AleksandrDneprCity/Pentagon-4096/Firmwares/PS2_Mouse/ATTiny2313/ZXKM4.PNG

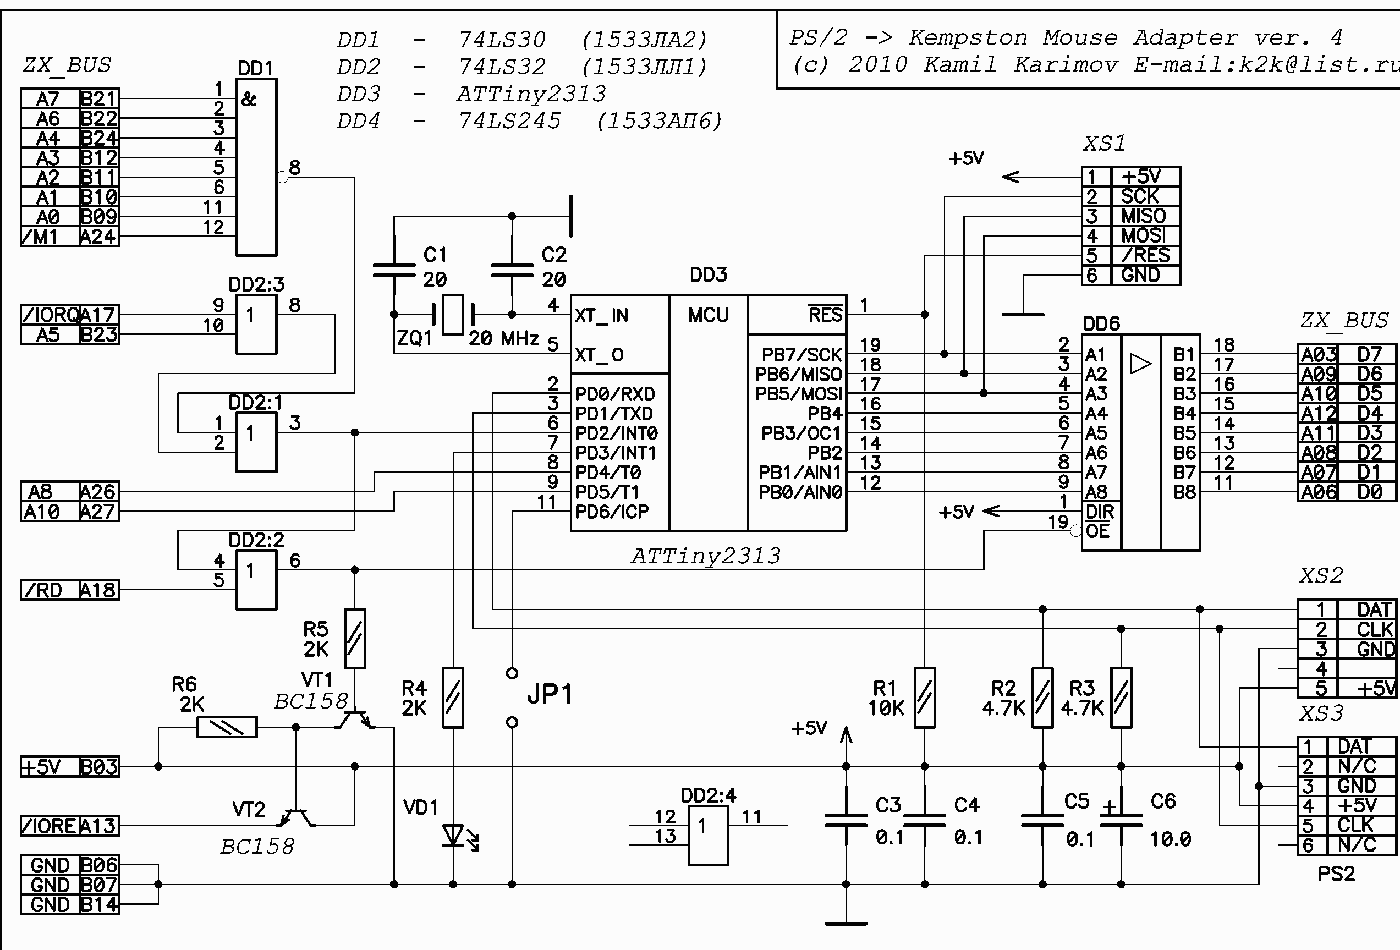
Firmwares/PS2_Mouse/ATTiny2313/ZXKM4.PNG
