AleksandrDneprCity/Pentagon-4096/H_Sign_Multisim.png

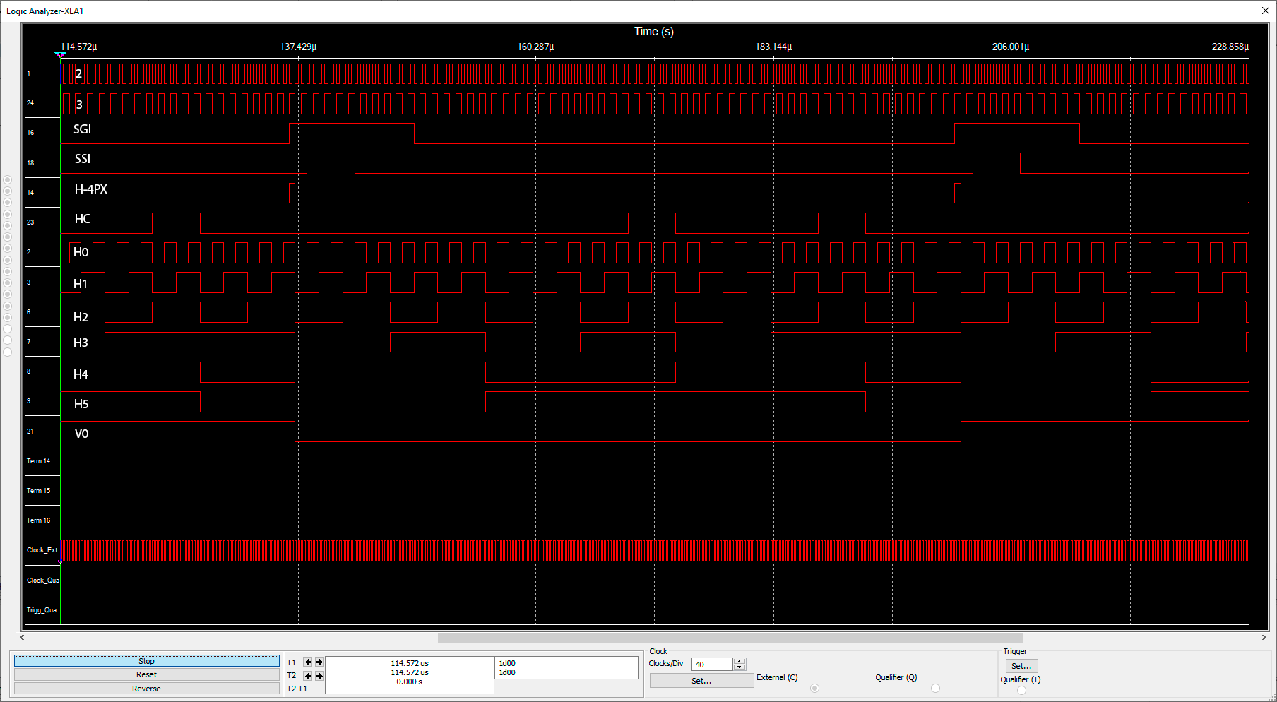
H_Sign_Multisim.png
