AleksandrDneprCity/Pentagon-4096/Hardware/Export/PNG/FreqInd-v1-pcb-comp-bottom.png

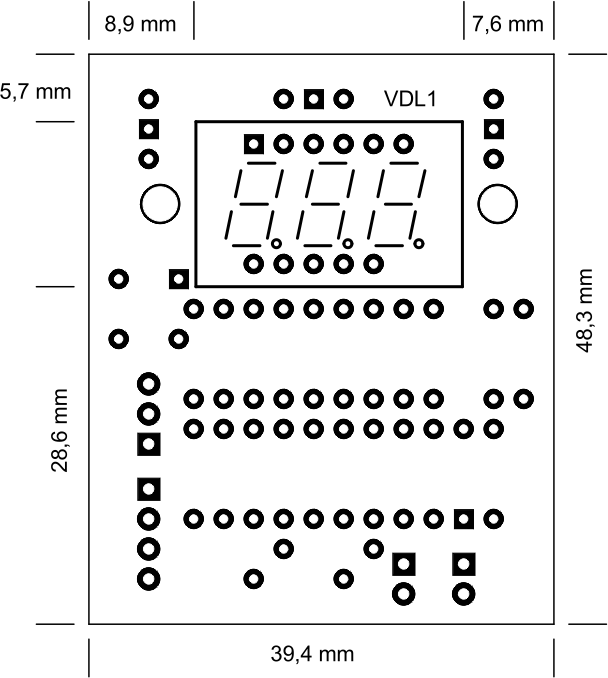
Hardware/Export/PNG/FreqInd-v1-pcb-comp-bottom.png
