AleksandrDneprCity/Pentagon-4096/Hardware/Export/PNG/FreqInd-v1-pcb-layer-bottom-fotores.png

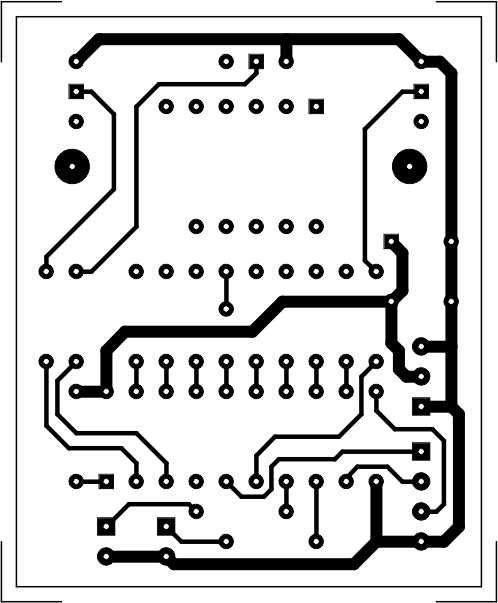
Hardware/Export/PNG/FreqInd-v1-pcb-layer-bottom-fotores.png
