AleksandrDneprCity/Pentagon-4096/Hardware/Export/PNG/FreqInd-v2-pcb-comp-top.png

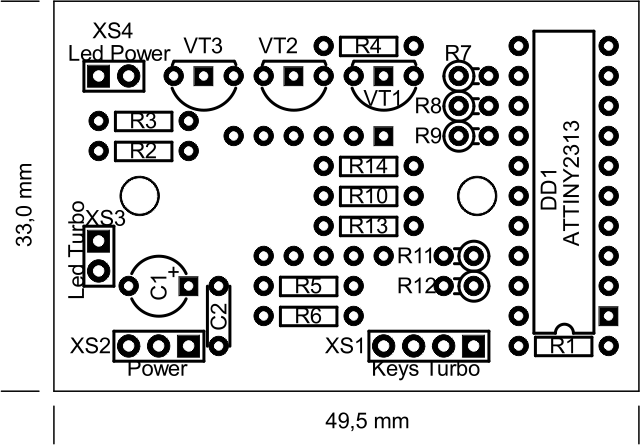
Hardware/Export/PNG/FreqInd-v2-pcb-comp-top.png
