AleksandrDneprCity/Pentagon-4096/Hardware/Export/PNG/FreqInd-v2-pcb-layer-bottom-fotores.png

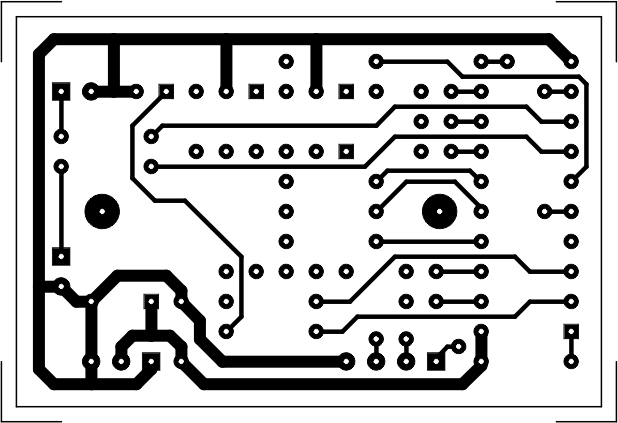
Hardware/Export/PNG/FreqInd-v2-pcb-layer-bottom-fotores.png
