AleksandrDneprCity/Pentagon-4096/Hardware/Export/PNG/FreqInd-v2-pcb-layer-top-fotores.png

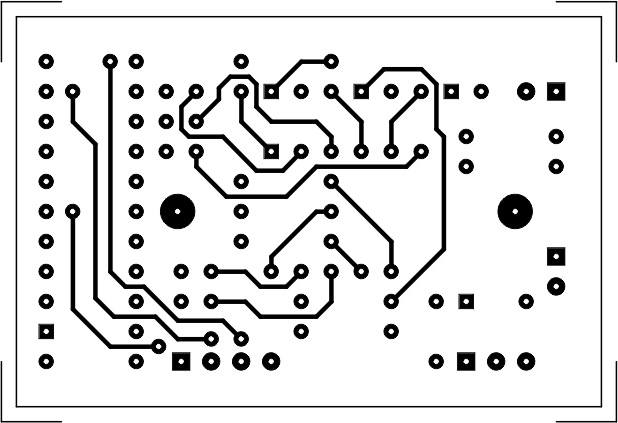
Hardware/Export/PNG/FreqInd-v2-pcb-layer-top-fotores.png
