AleksandrDneprCity/Pentagon-4096/Hardware/Export/PNG/FreqInd-v2-pcb-layer-top.png

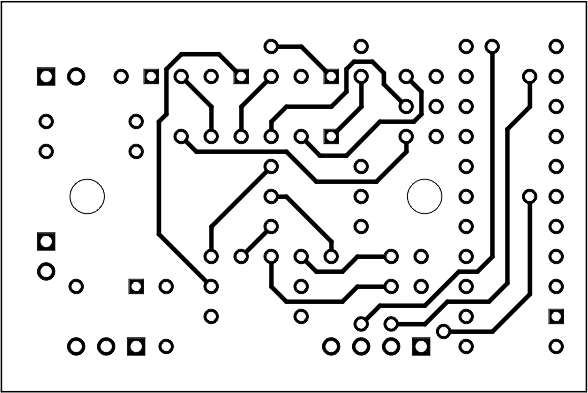
Hardware/Export/PNG/FreqInd-v2-pcb-layer-top.png
