AleksandrDneprCity/Pentagon-4096/Hardware/Export/PNG/MainBoard-v10.7-pcb-layer-bottom.png

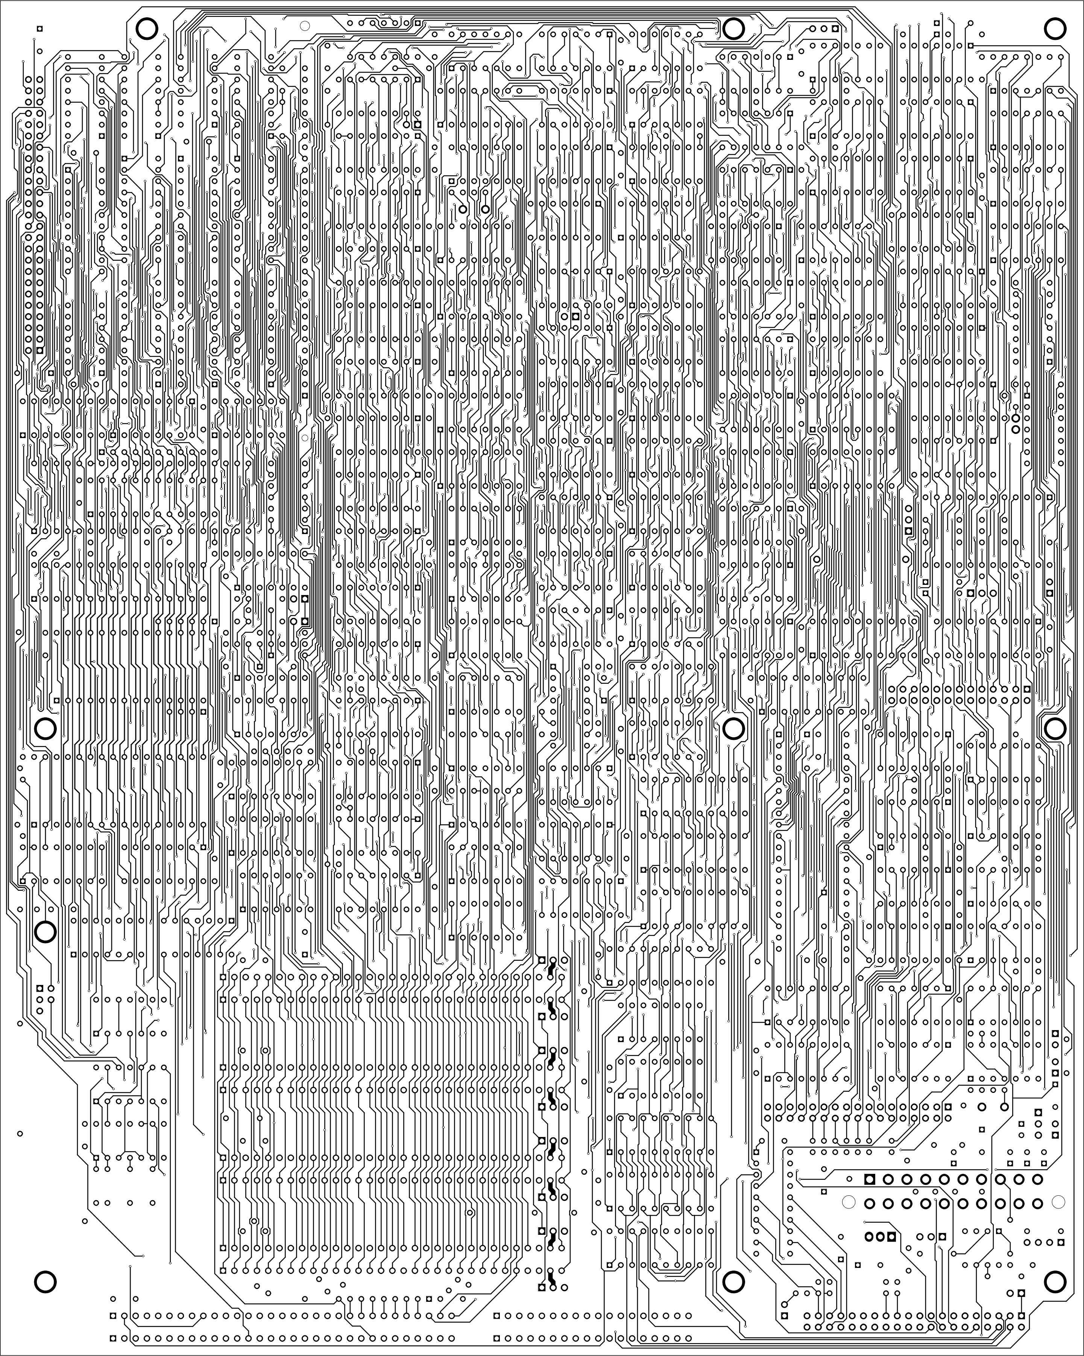
Hardware/Export/PNG/MainBoard-v10.7-pcb-layer-bottom.png
