AleksandrDneprCity/Pentagon-4096/Hardware/Export/PNG/MainBoard-v10.7-pcb-layer-gnd.png

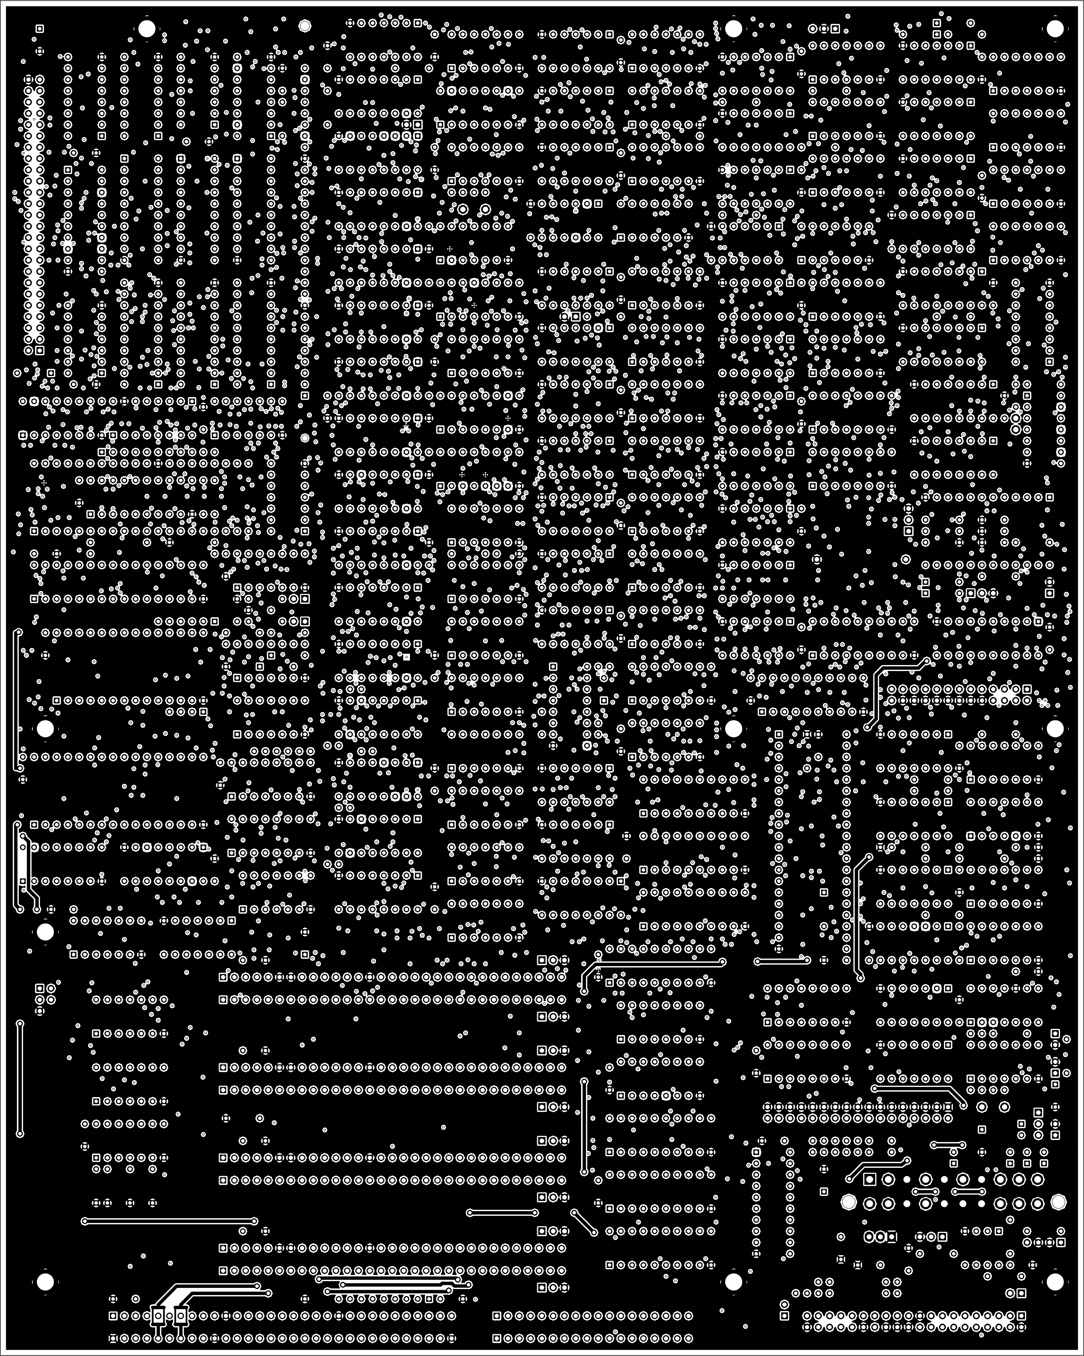
Hardware/Export/PNG/MainBoard-v10.7-pcb-layer-gnd.png
