AleksandrDneprCity/Pentagon-4096/Hardware/Export/PNG/MainBoard-v10.7-pcb-layer-power.png

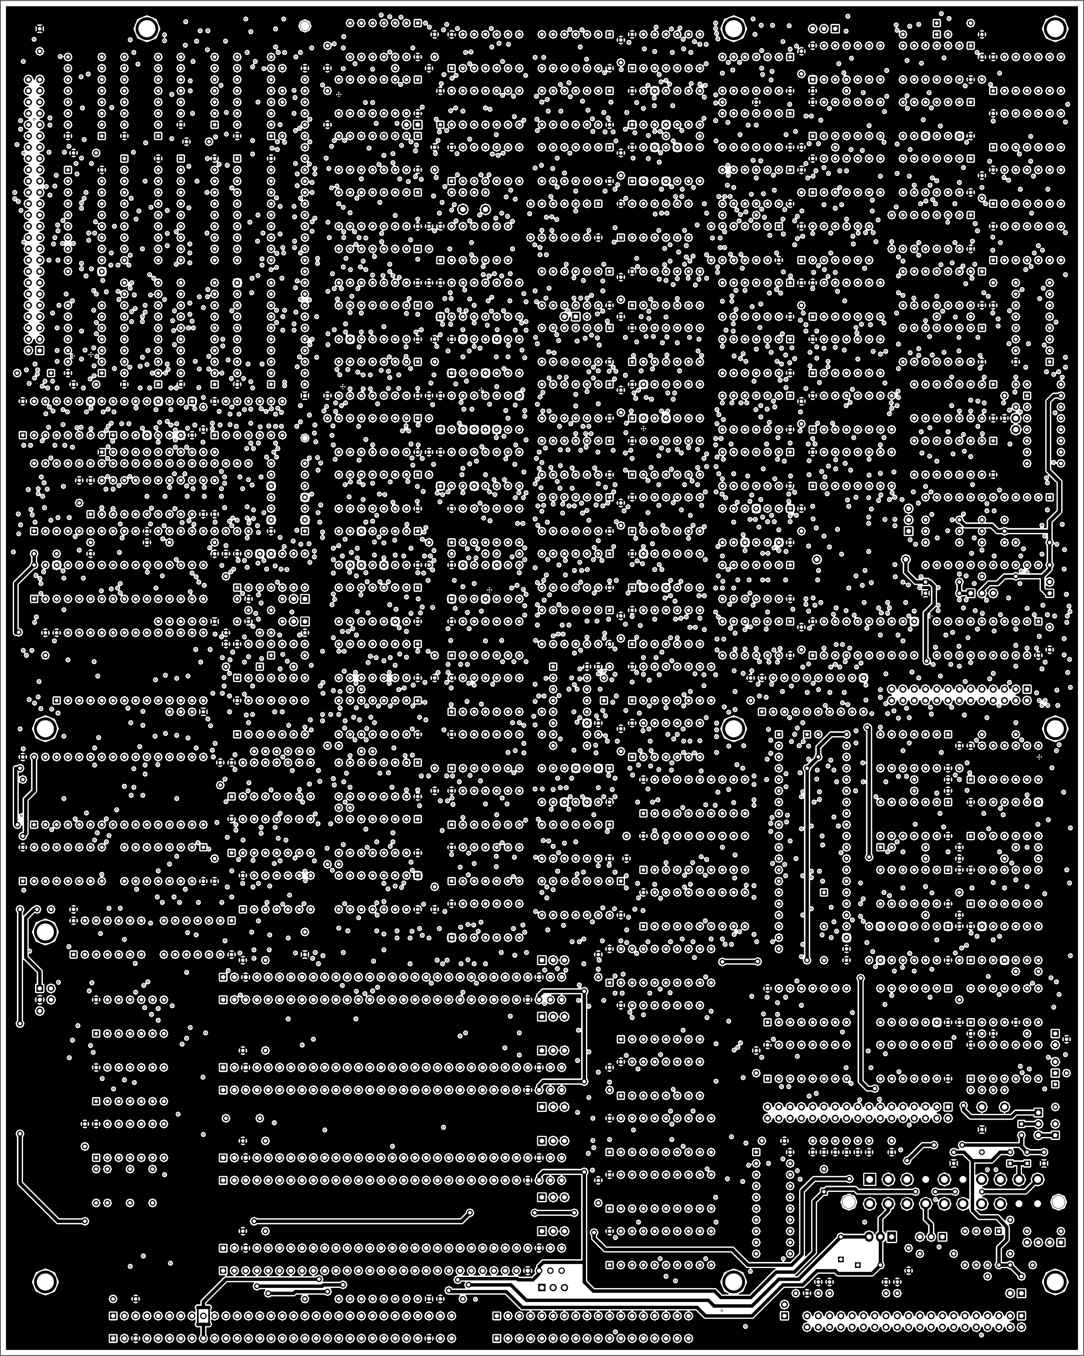
Hardware/Export/PNG/MainBoard-v10.7-pcb-layer-power.png
