AleksandrDneprCity/Pentagon-4096/Hardware/Export/PNG/NemoBusToDivIDE-v1.3-pcb-layer-top.png

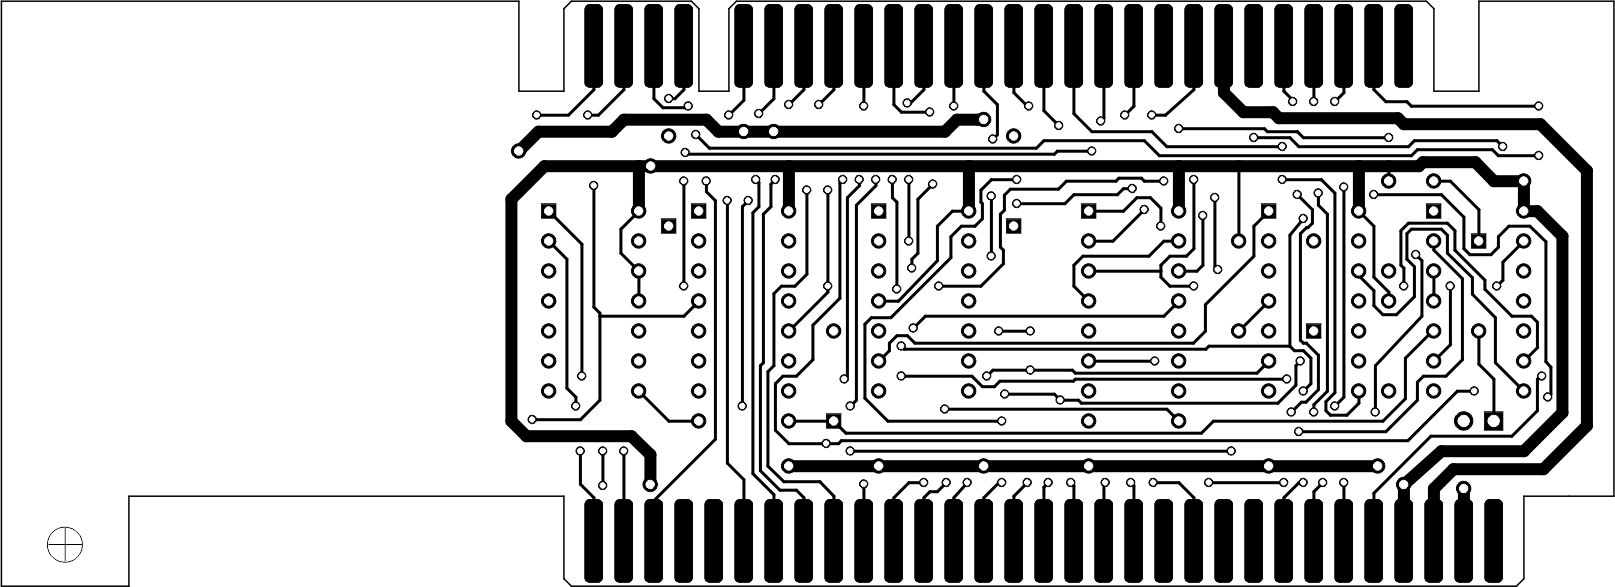
Hardware/Export/PNG/NemoBusToDivIDE-v1.3-pcb-layer-top.png
