AleksandrDneprCity/Pentagon-4096/Hardware/Export/PNG/TopBoard-v5.3-pcb-comp-top.png

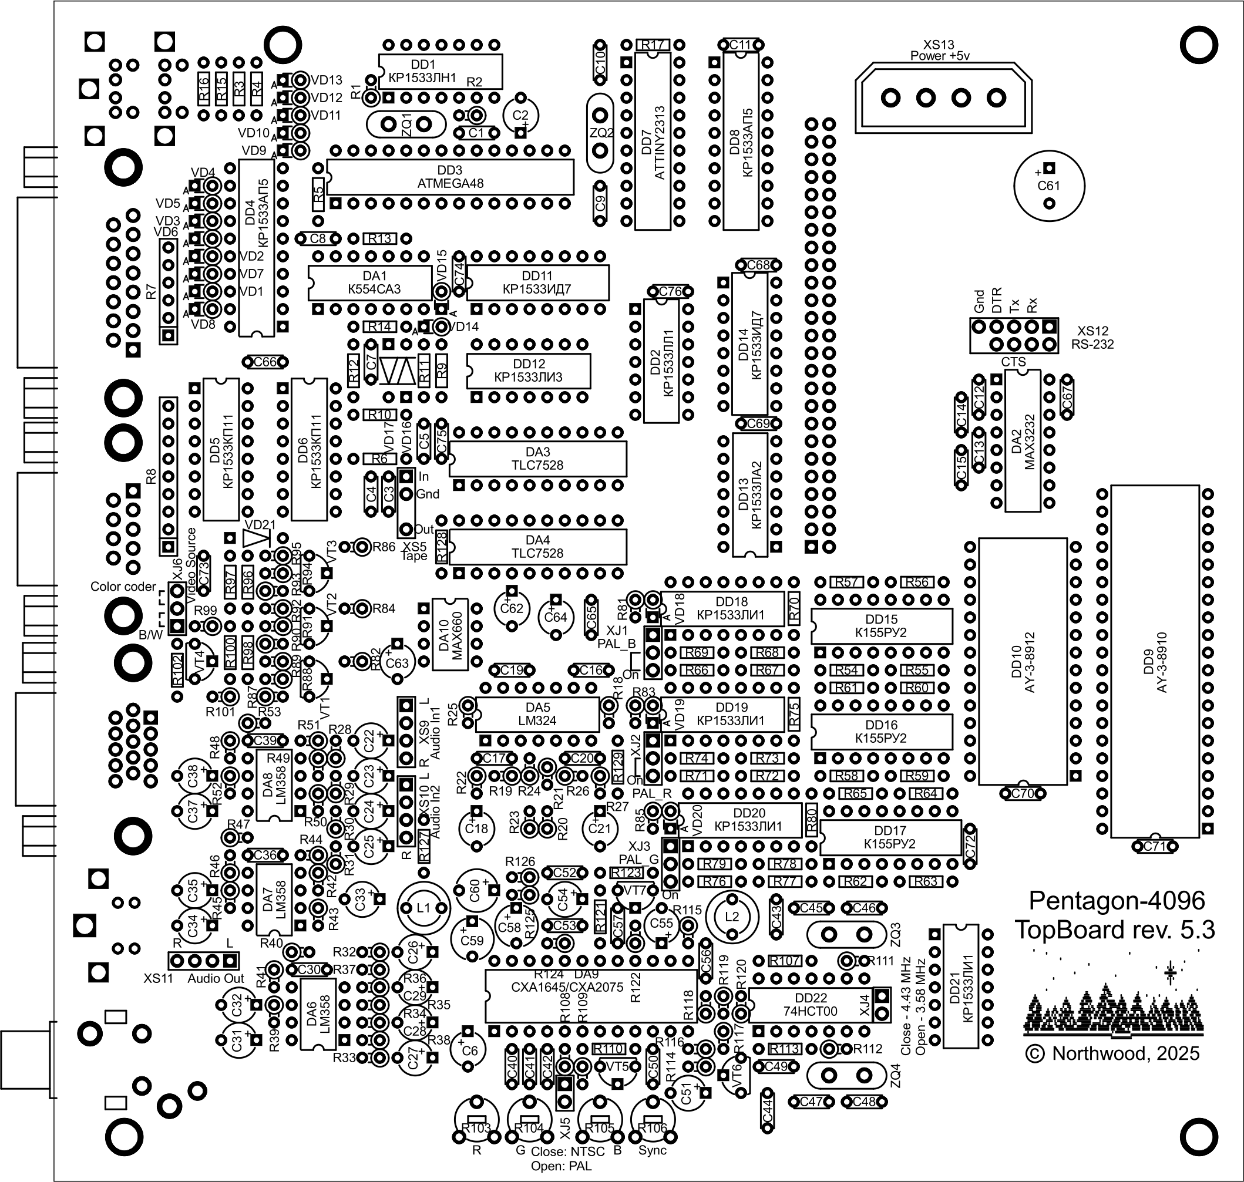
Hardware/Export/PNG/TopBoard-v5.3-pcb-comp-top.png
