AleksandrDneprCity/Pentagon-4096/Hardware/Export/PNG/TopBoard-v5.3-pcb-layer-bottom.png

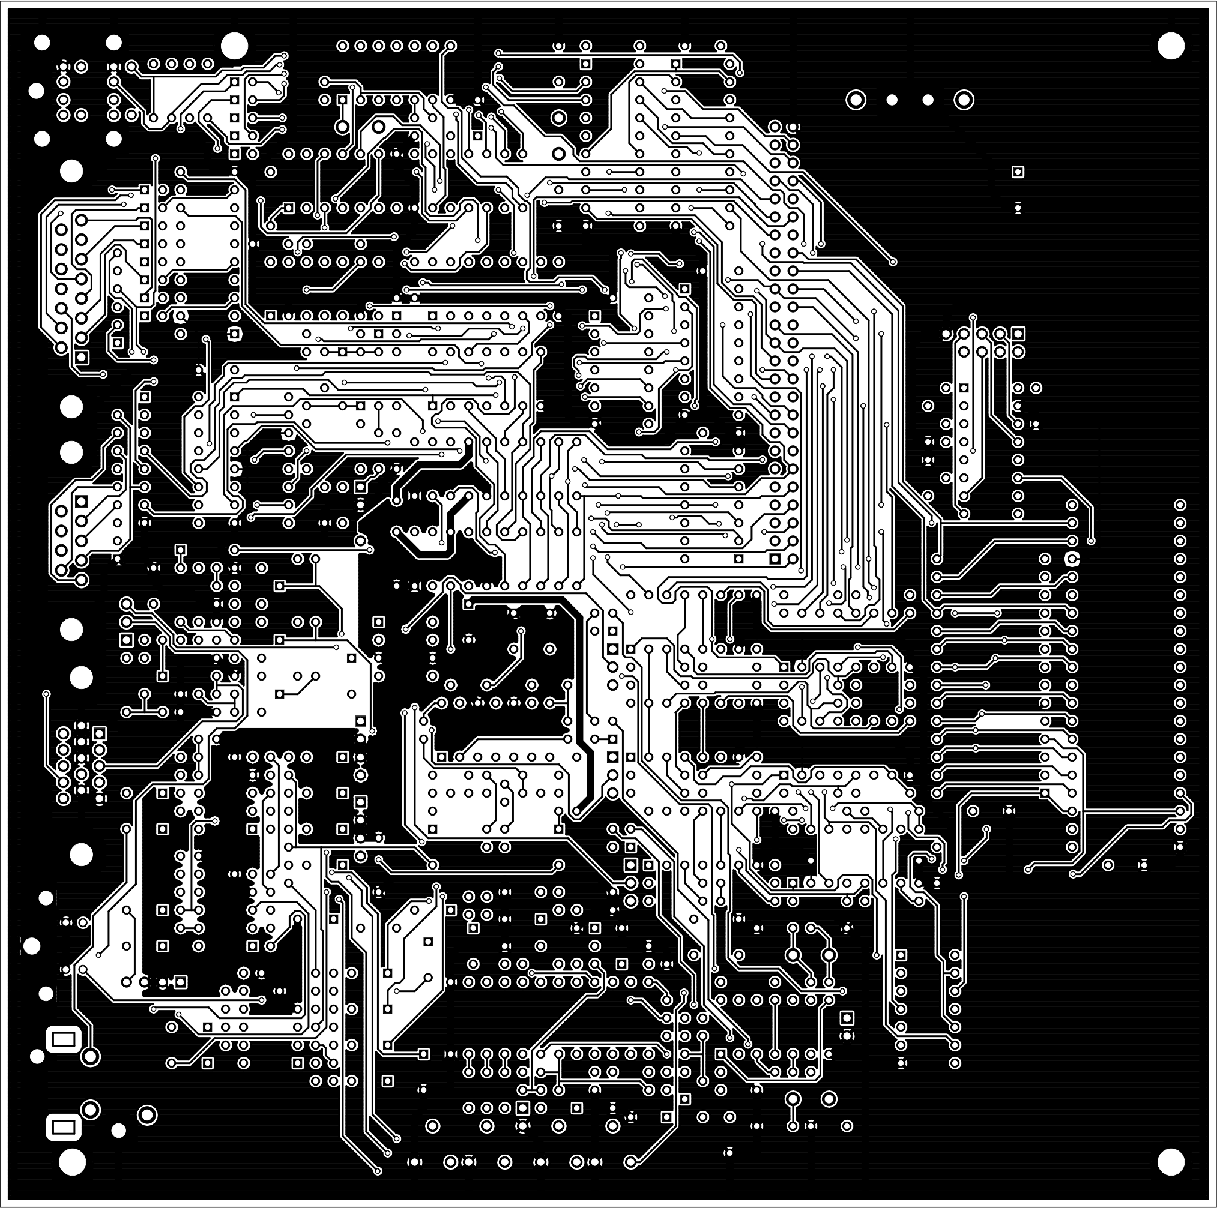
Hardware/Export/PNG/TopBoard-v5.3-pcb-layer-bottom.png
