AleksandrDneprCity/Pentagon-4096/Hardware/Export/PNG/TopBoard-v5.3-sch.png

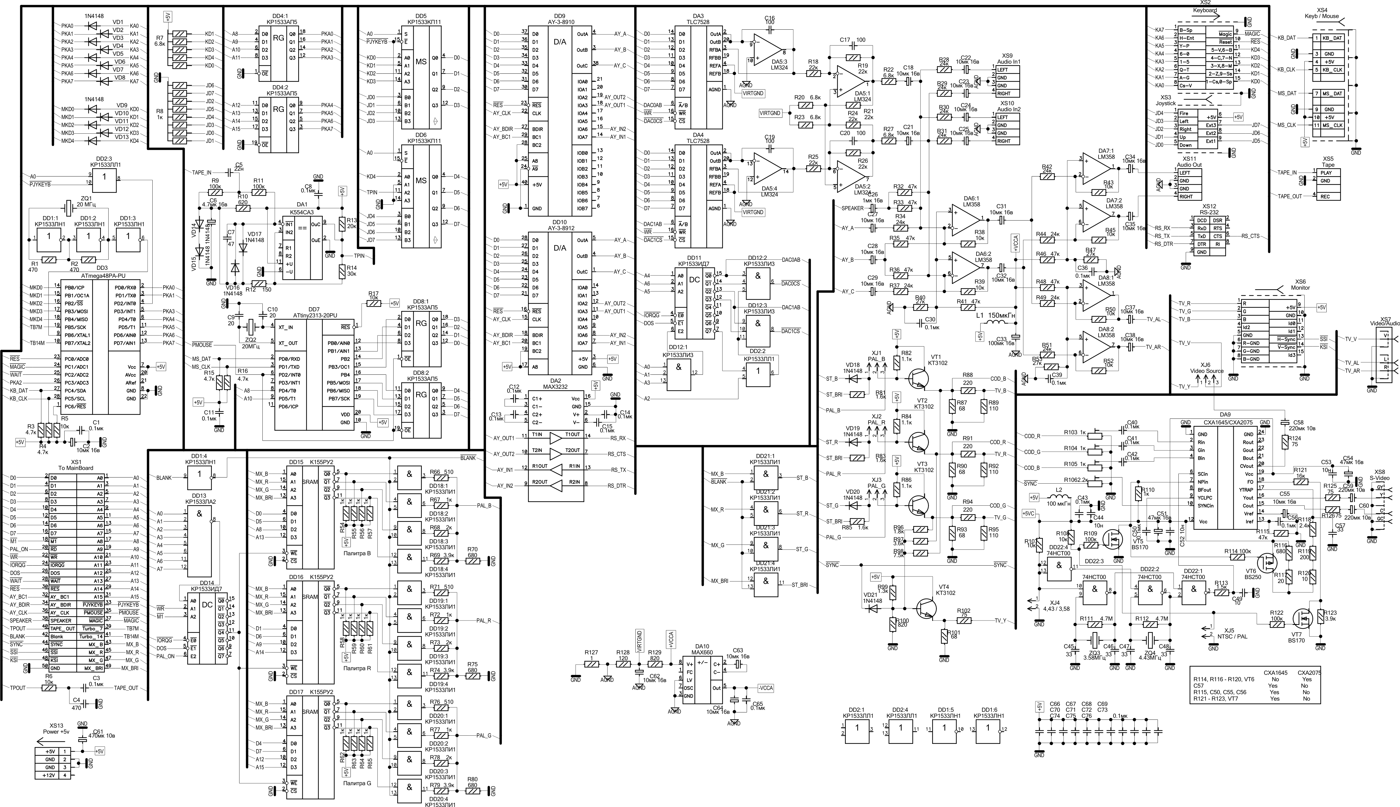
Hardware/Export/PNG/TopBoard-v5.3-sch.png
