AleksandrDneprCity/Pentagon-4096/V_Sign-1_Multisim.png

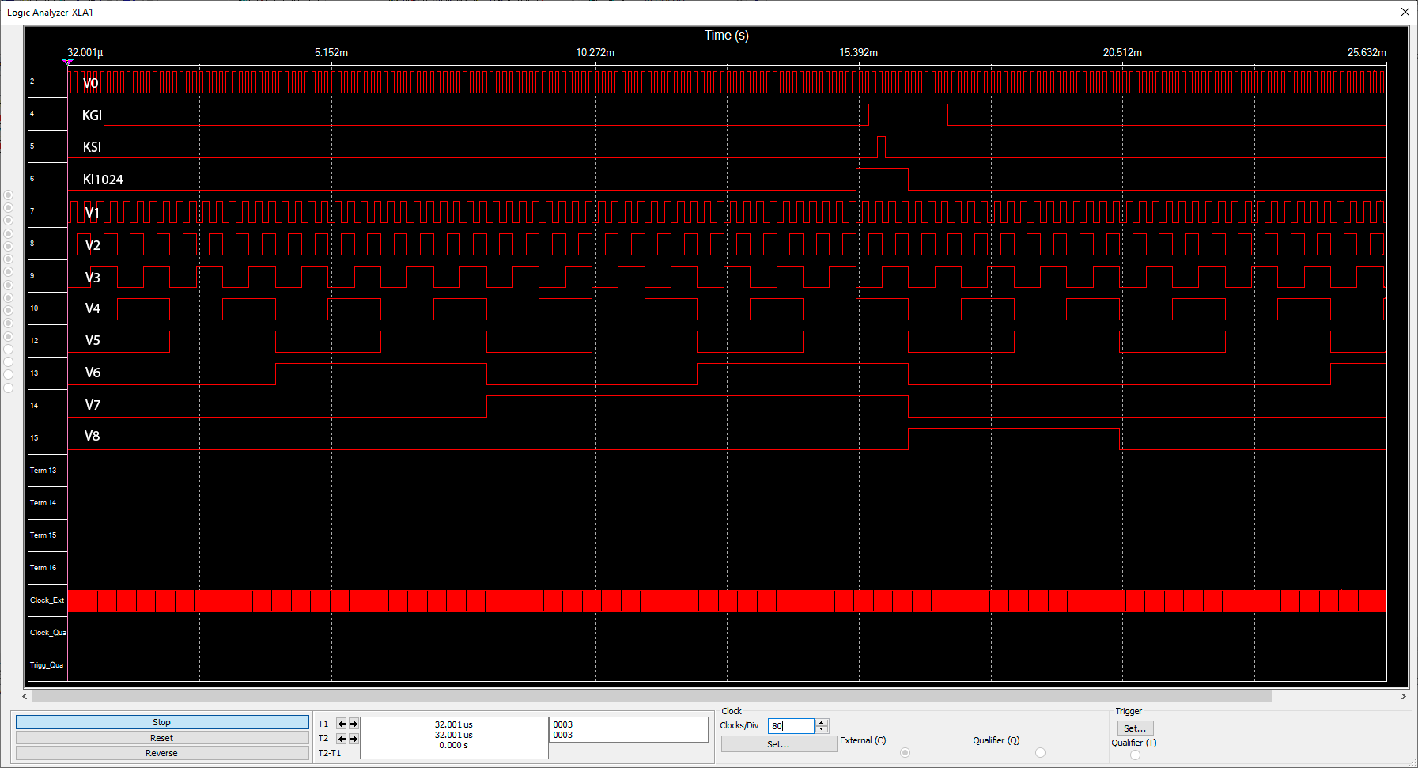
V_Sign-1_Multisim.png
