AleksandrDneprCity/Pentagon-4096/V_Sign-2_Multisim.png

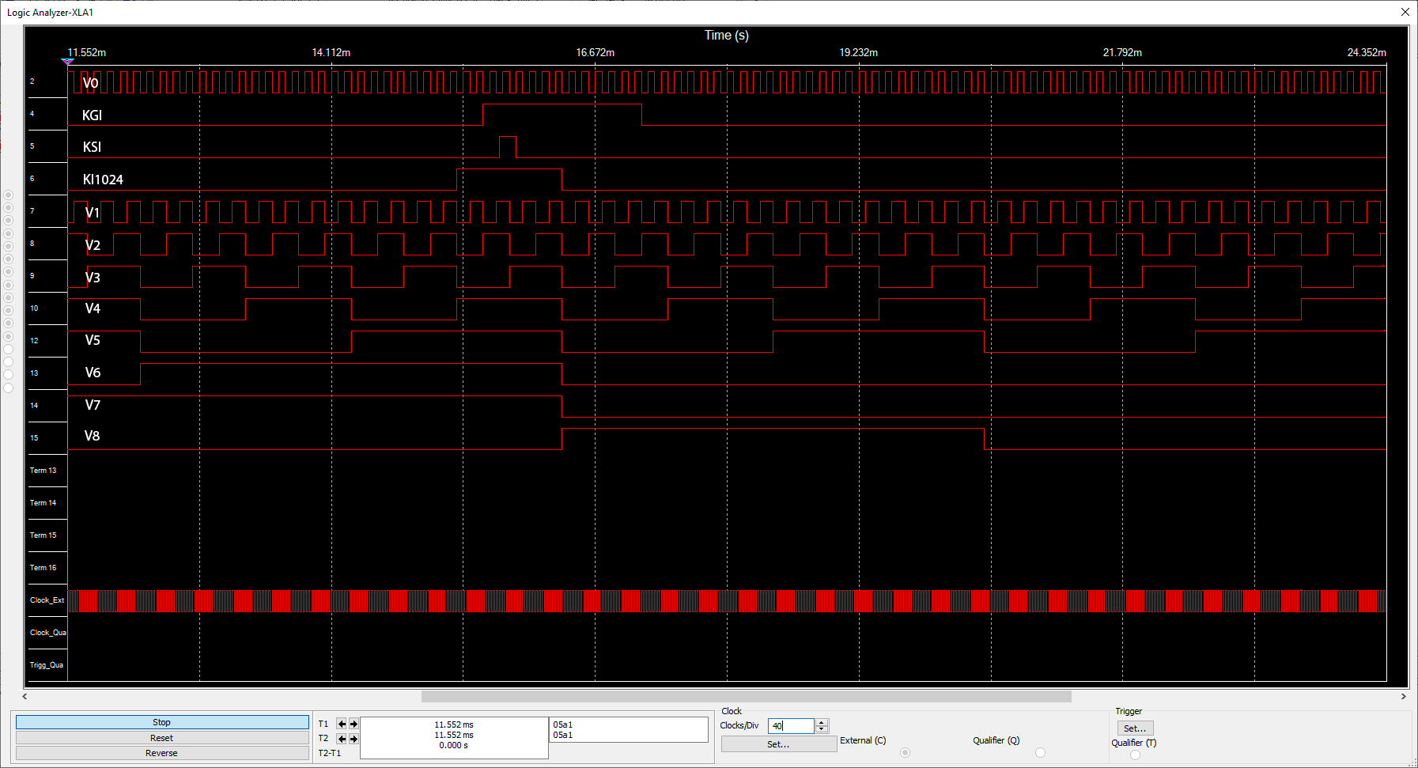
V_Sign-2_Multisim.png
