AleksandrDneprCity/Pentagon-4096/Hardware/Export/PDF/FreqInd-sch.pdf

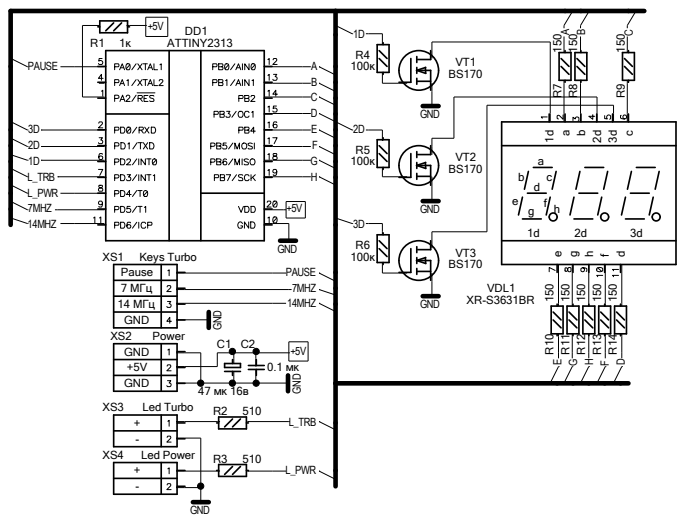
[picture p32: page 1]

Pause
7 МГц
14 МГц
GND

+5V
