AleksandrDneprCity/Pentagon-4096/Hardware/Export/PDF/NemoBusToDivIDE-v1.3-pcb-layer-bottom.pdf

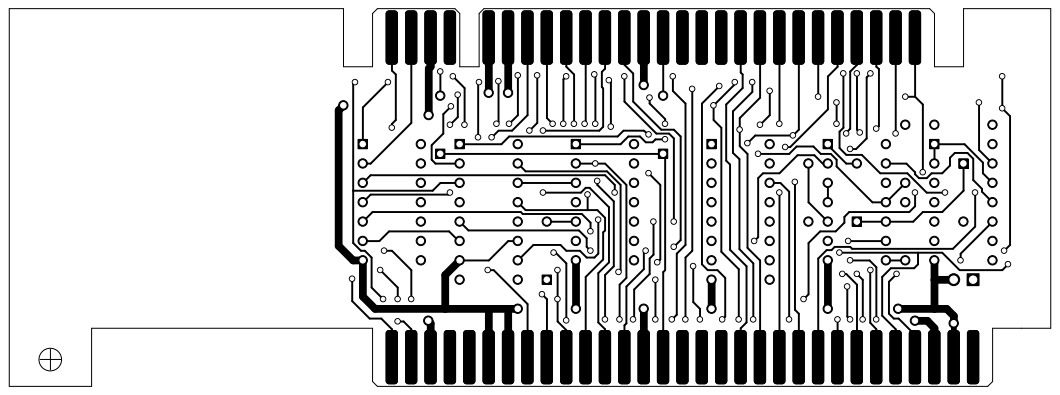
[picture p45: page 1]
