AleksandrDneprCity/Pentagon-4096/Hardware/Export/PDF/NemoBusToDivIDE-v1.3-pcb-layer-top.pdf

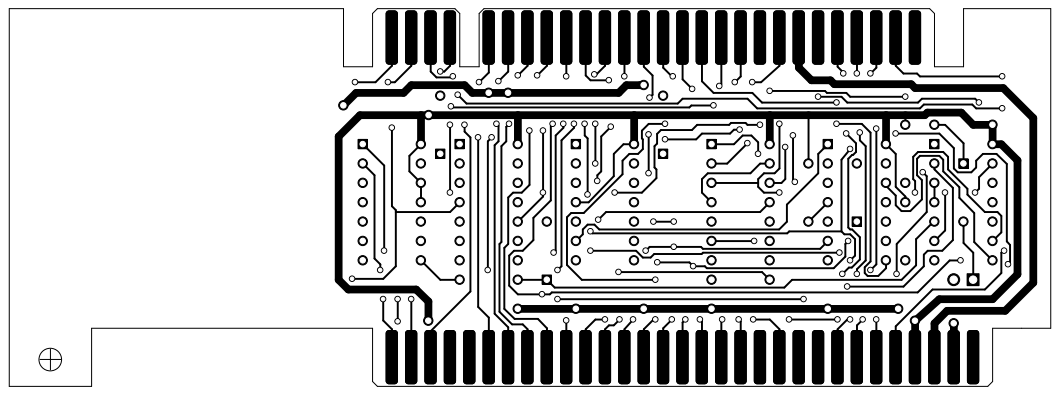
[picture p46: page 1]
