AleksandrDneprCity/Pentagon-4096/Hardware/Export/PDF/NemoBusToDivIDE-v1.3-sch.pdf

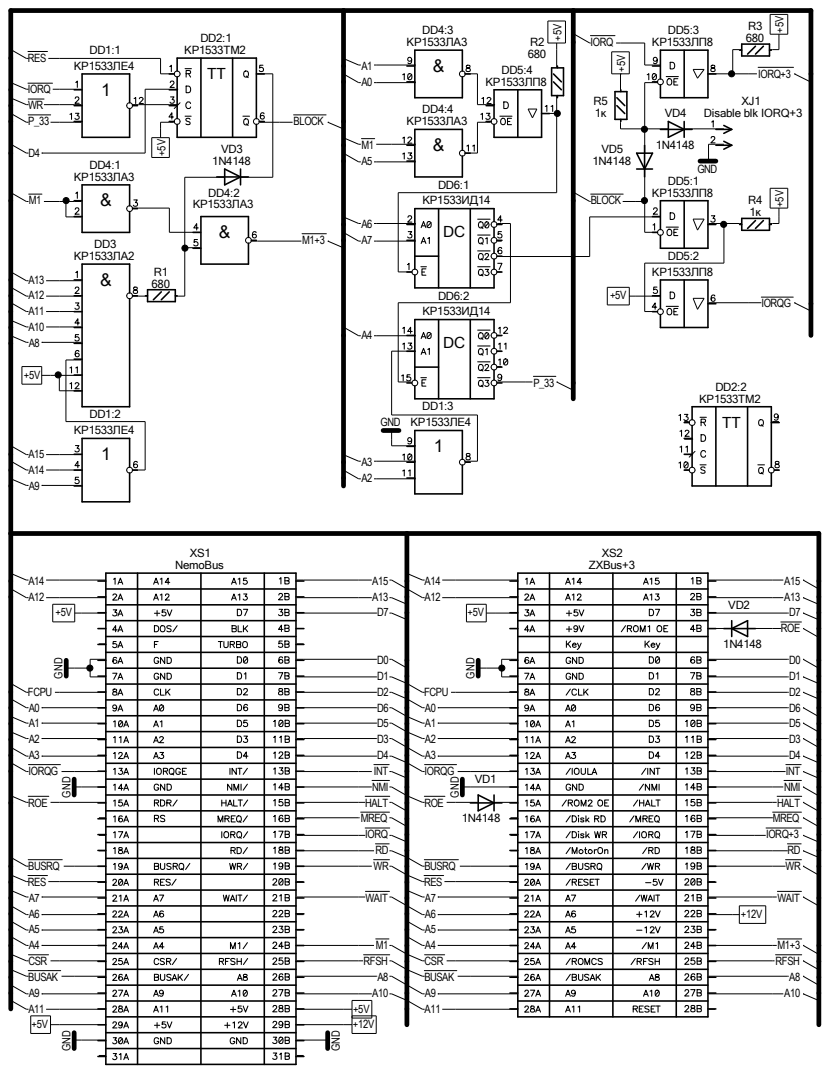
[picture p47: page 1]
