AleksandrDneprCity/Pentagon-4096/Hardware/Export/PDF/FreqInd-v2-pcb-comp-bottom.pdf

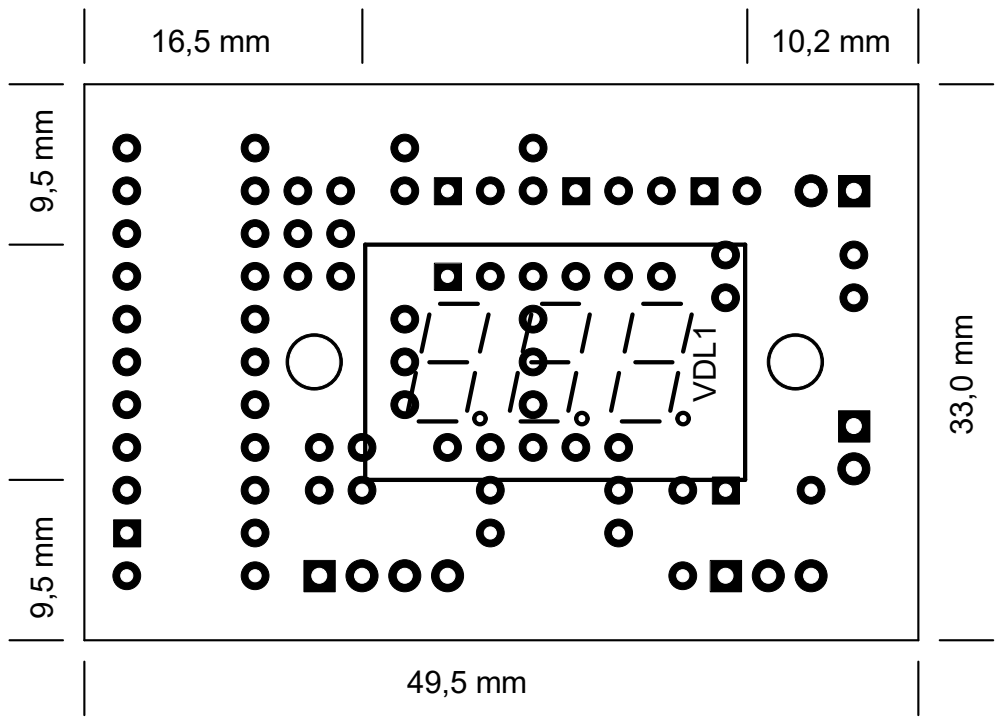
[picture p48: page 1]
VDL1
