AleksandrDneprCity/Pentagon-4096/Hardware/Export/PDF/FreqInd-v2-pcb-comp-top.pdf

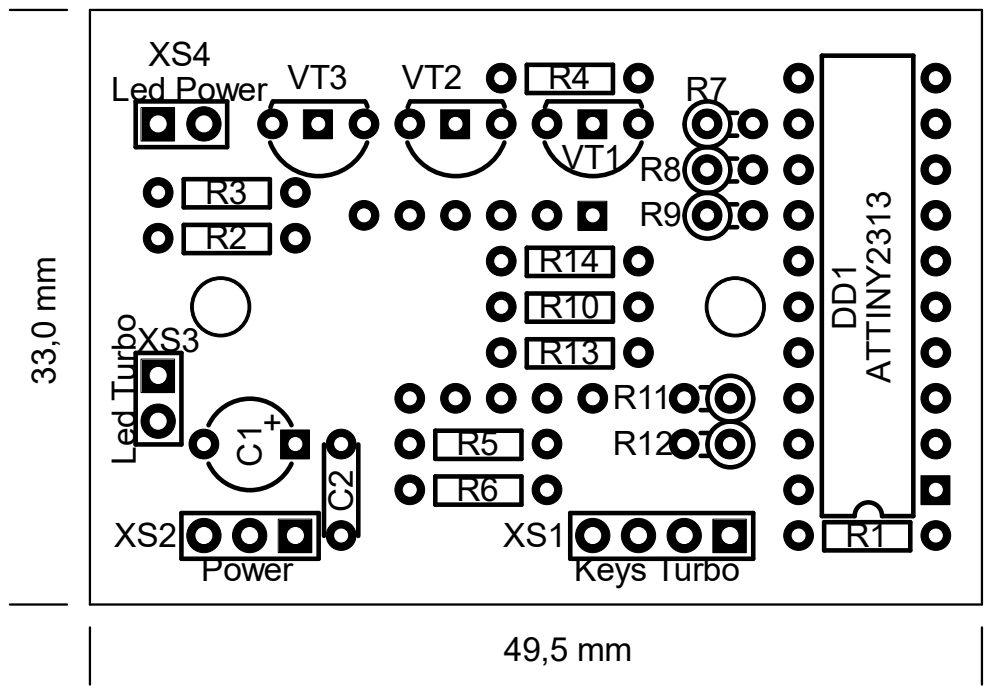
[picture p49: page 1]
