AleksandrDneprCity/Pentagon-4096/Hardware/Export/PDF/FreqInd-v2-pcb-layer-bottom-fotores.pdf

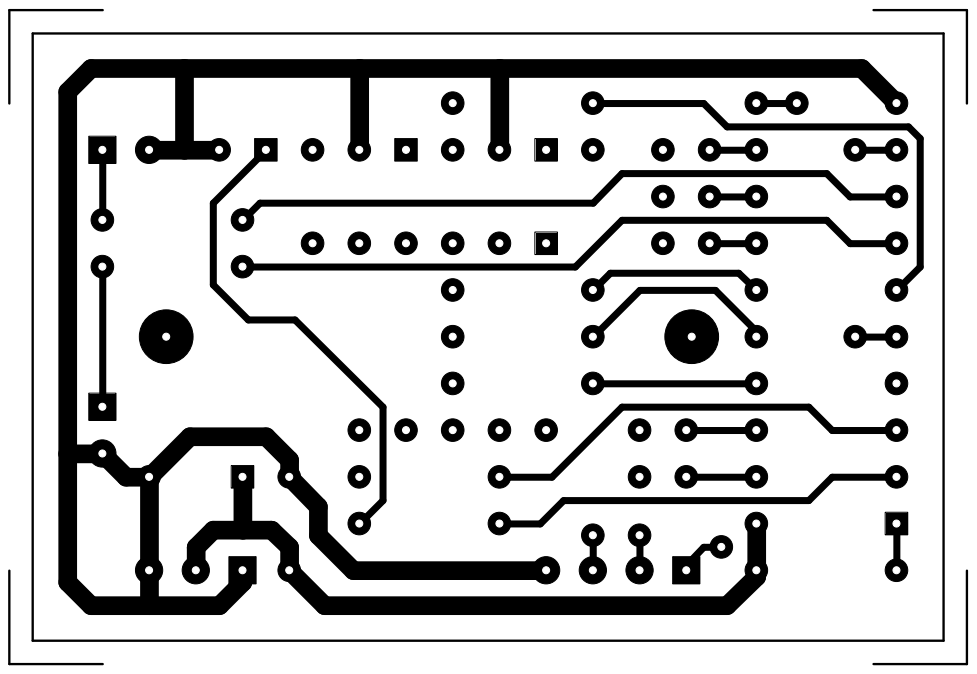
[picture p50: page 1]
