AleksandrDneprCity/Pentagon-4096/Hardware/Export/PDF/FreqInd-v2-pcb-layer-bottom.pdf

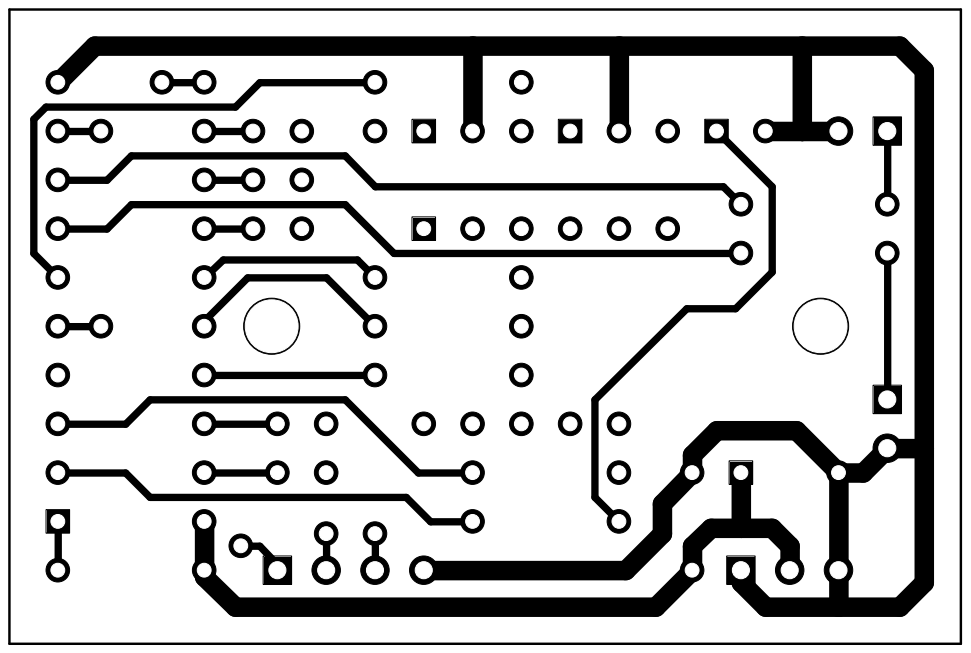
[picture p51: page 1]
