AleksandrDneprCity/Pentagon-4096/Hardware/Export/PDF/FreqInd-v2-pcb-layer-top-fotores.pdf

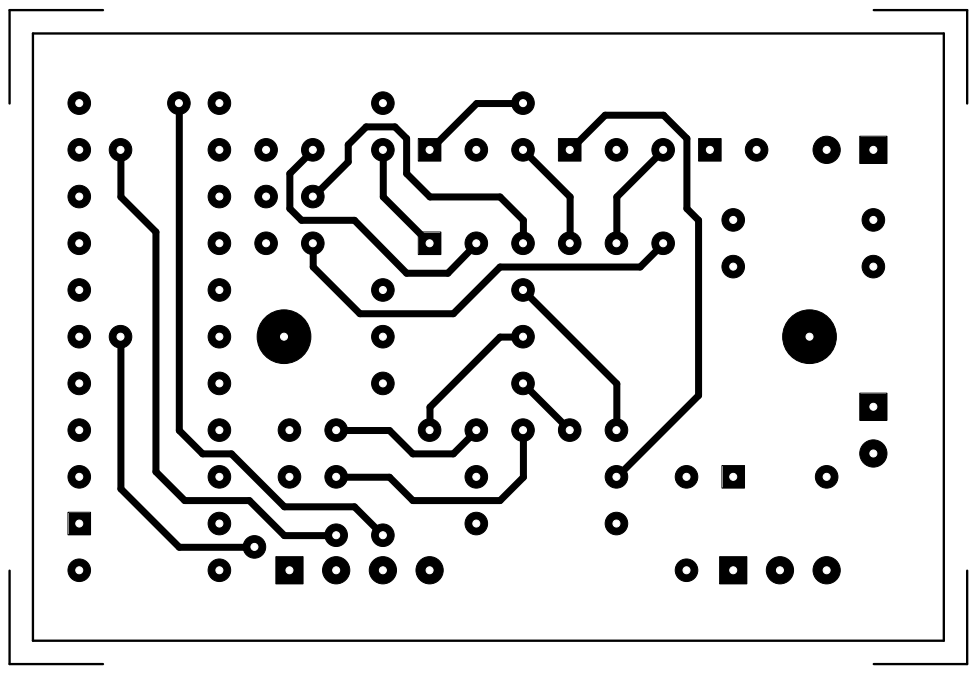
[picture p52: page 1]
