AleksandrDneprCity/Pentagon-4096/Hardware/Export/PDF/FreqInd-v2-pcb-layer-top.pdf

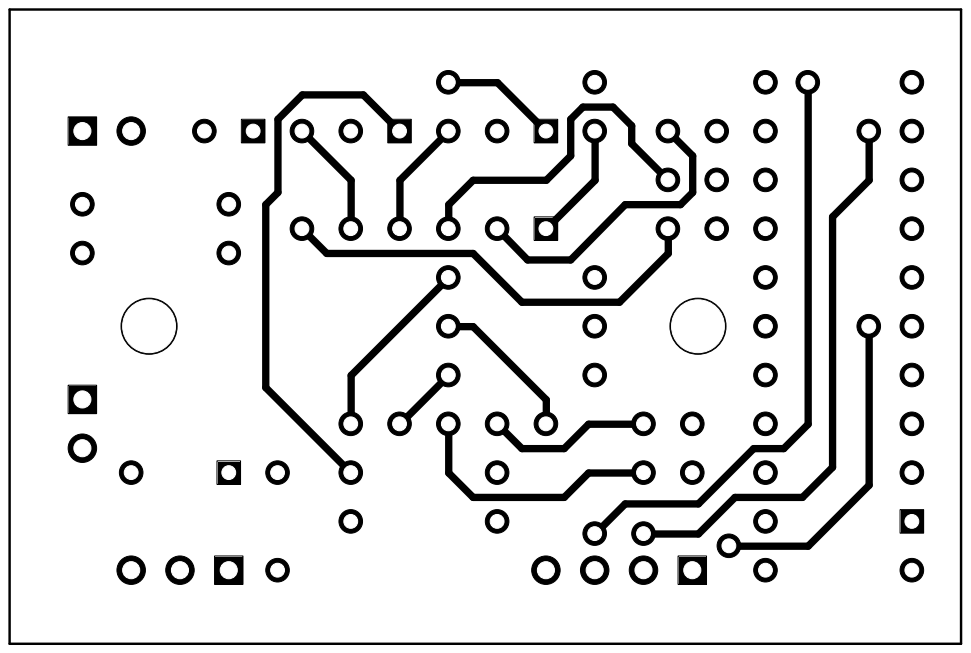
[picture p53: page 1]
