AleksandrDneprCity/Pentagon-4096/Hardware/Export/PDF/FreqInd-v1-pcb-comp-bottom.pdf

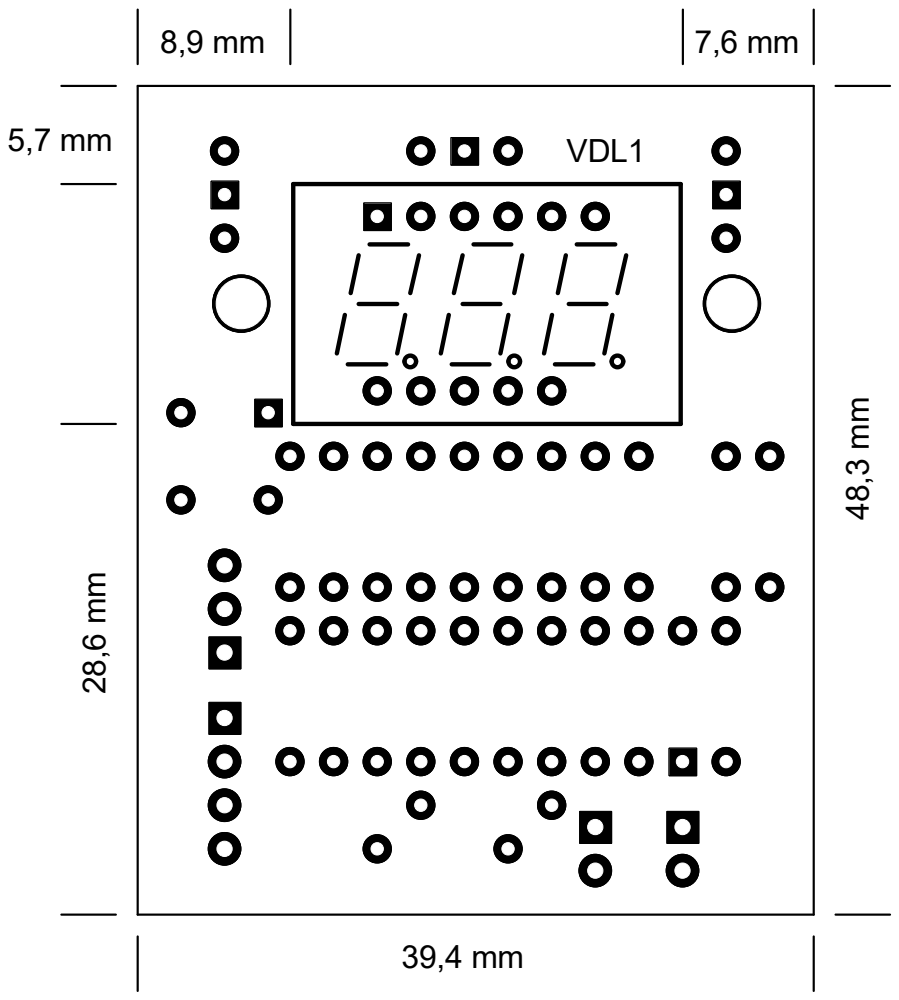
[picture p54: page 1]
VDL1
