AleksandrDneprCity/Pentagon-4096/Hardware/Export/PDF/FreqInd-v1-pcb-comp-top.pdf

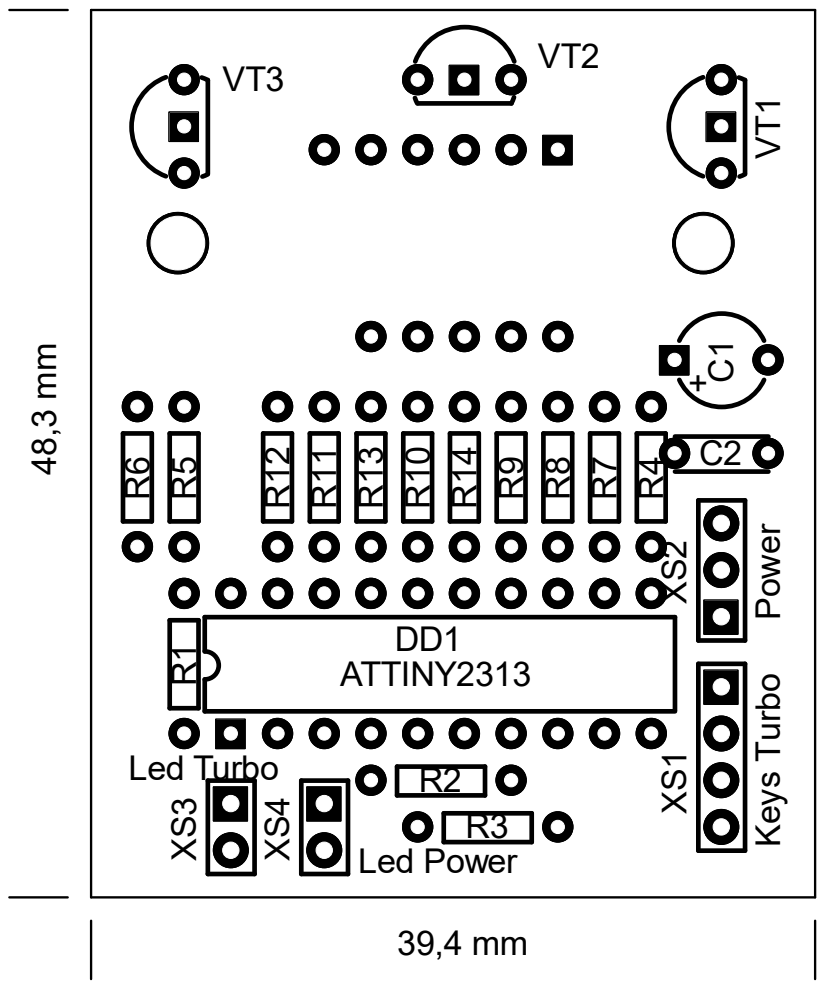
[picture p55: page 1]
