AleksandrDneprCity/Pentagon-4096/Hardware/Export/PDF/FreqInd-v1-pcb-layer-bottom-fotores.pdf

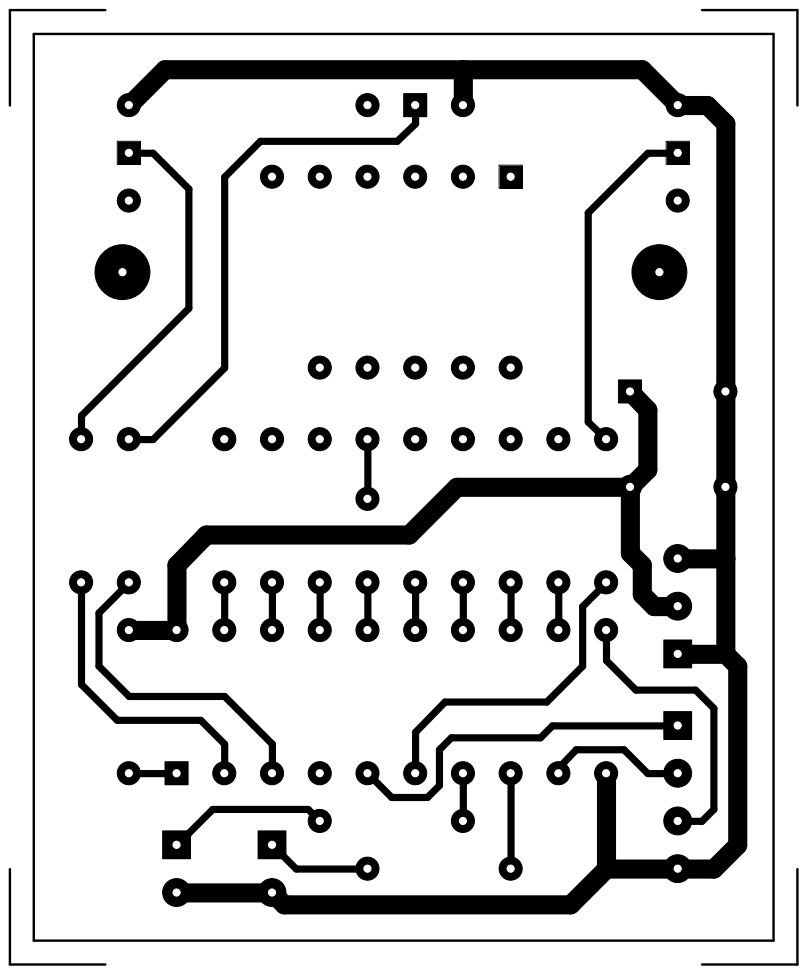
[picture p56: page 1]
