AleksandrDneprCity/Pentagon-4096/Hardware/Export/PDF/FreqInd-v1-pcb-layer-bottom.pdf

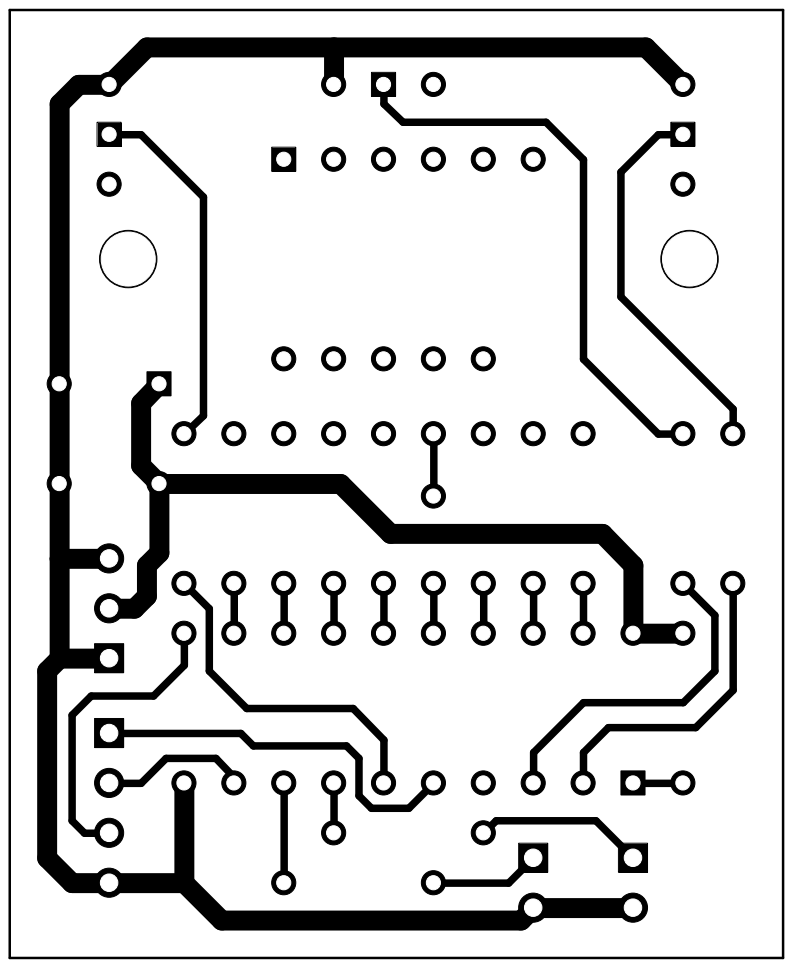
[picture p57: page 1]
