AleksandrDneprCity/Pentagon-4096/Hardware/Export/PDF/FreqInd-v1-pcb-layer-top-fotores.pdf

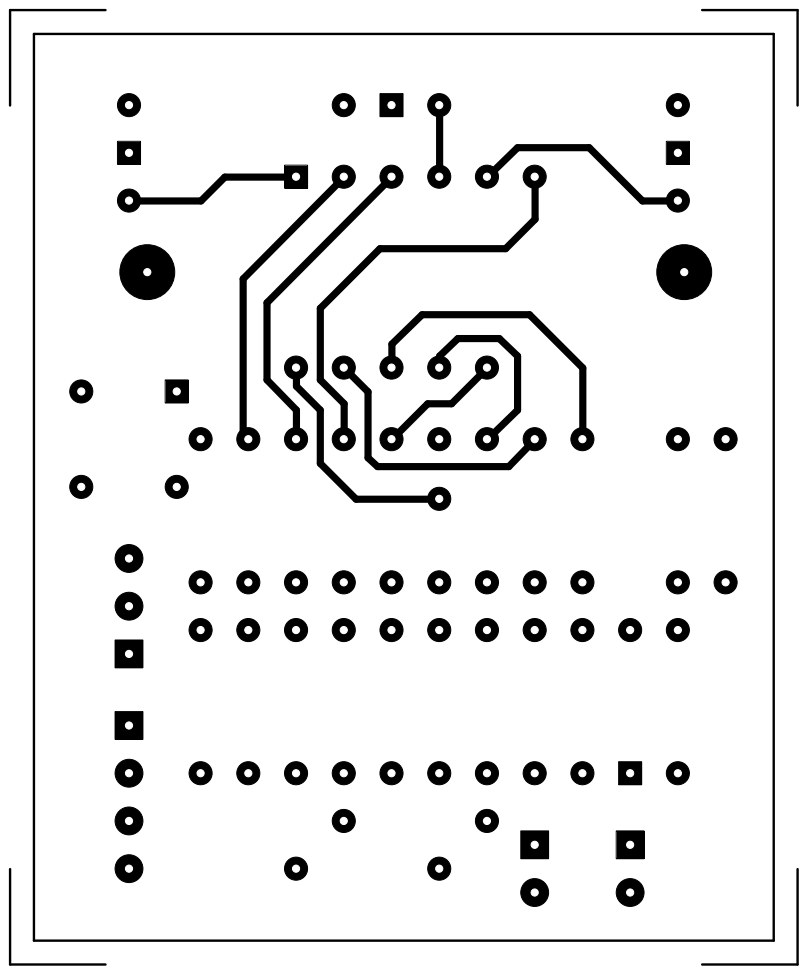
[picture p58: page 1]
