AleksandrDneprCity/Pentagon-4096/Hardware/Export/PDF/FreqInd-v1-pcb-layer-top.pdf

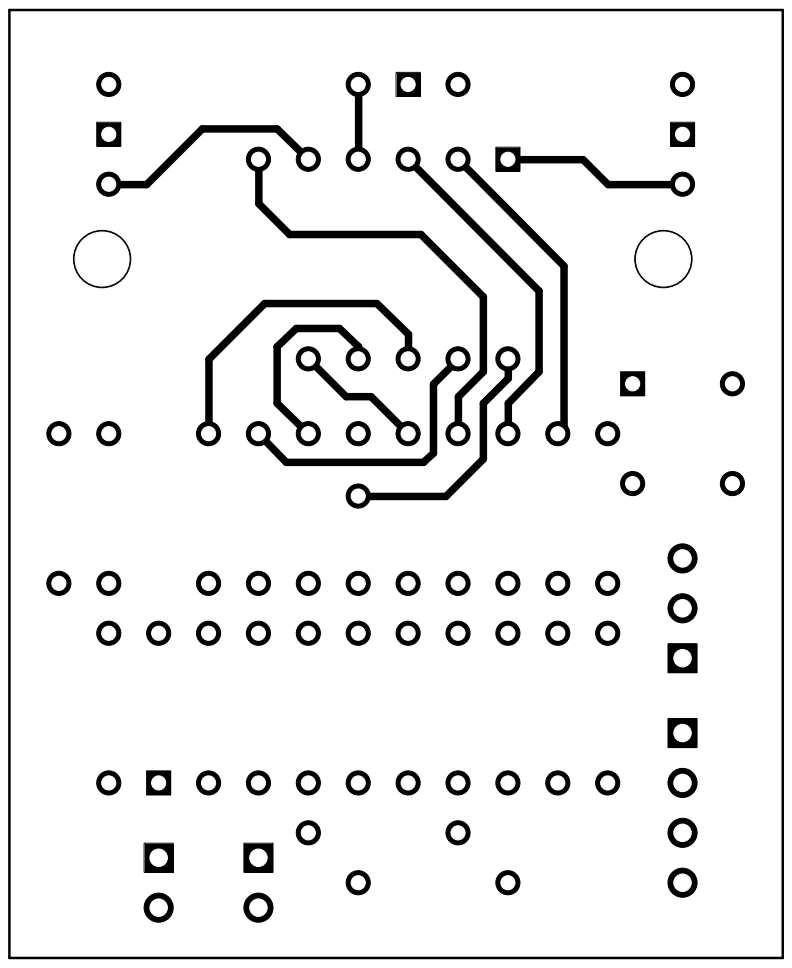
[picture p59: page 1]
